e4ch/elm2/kicad/Mainboard.kicad_sch

## KiCad design kicad/Mainboard.kicad_sch (2026-03-01)

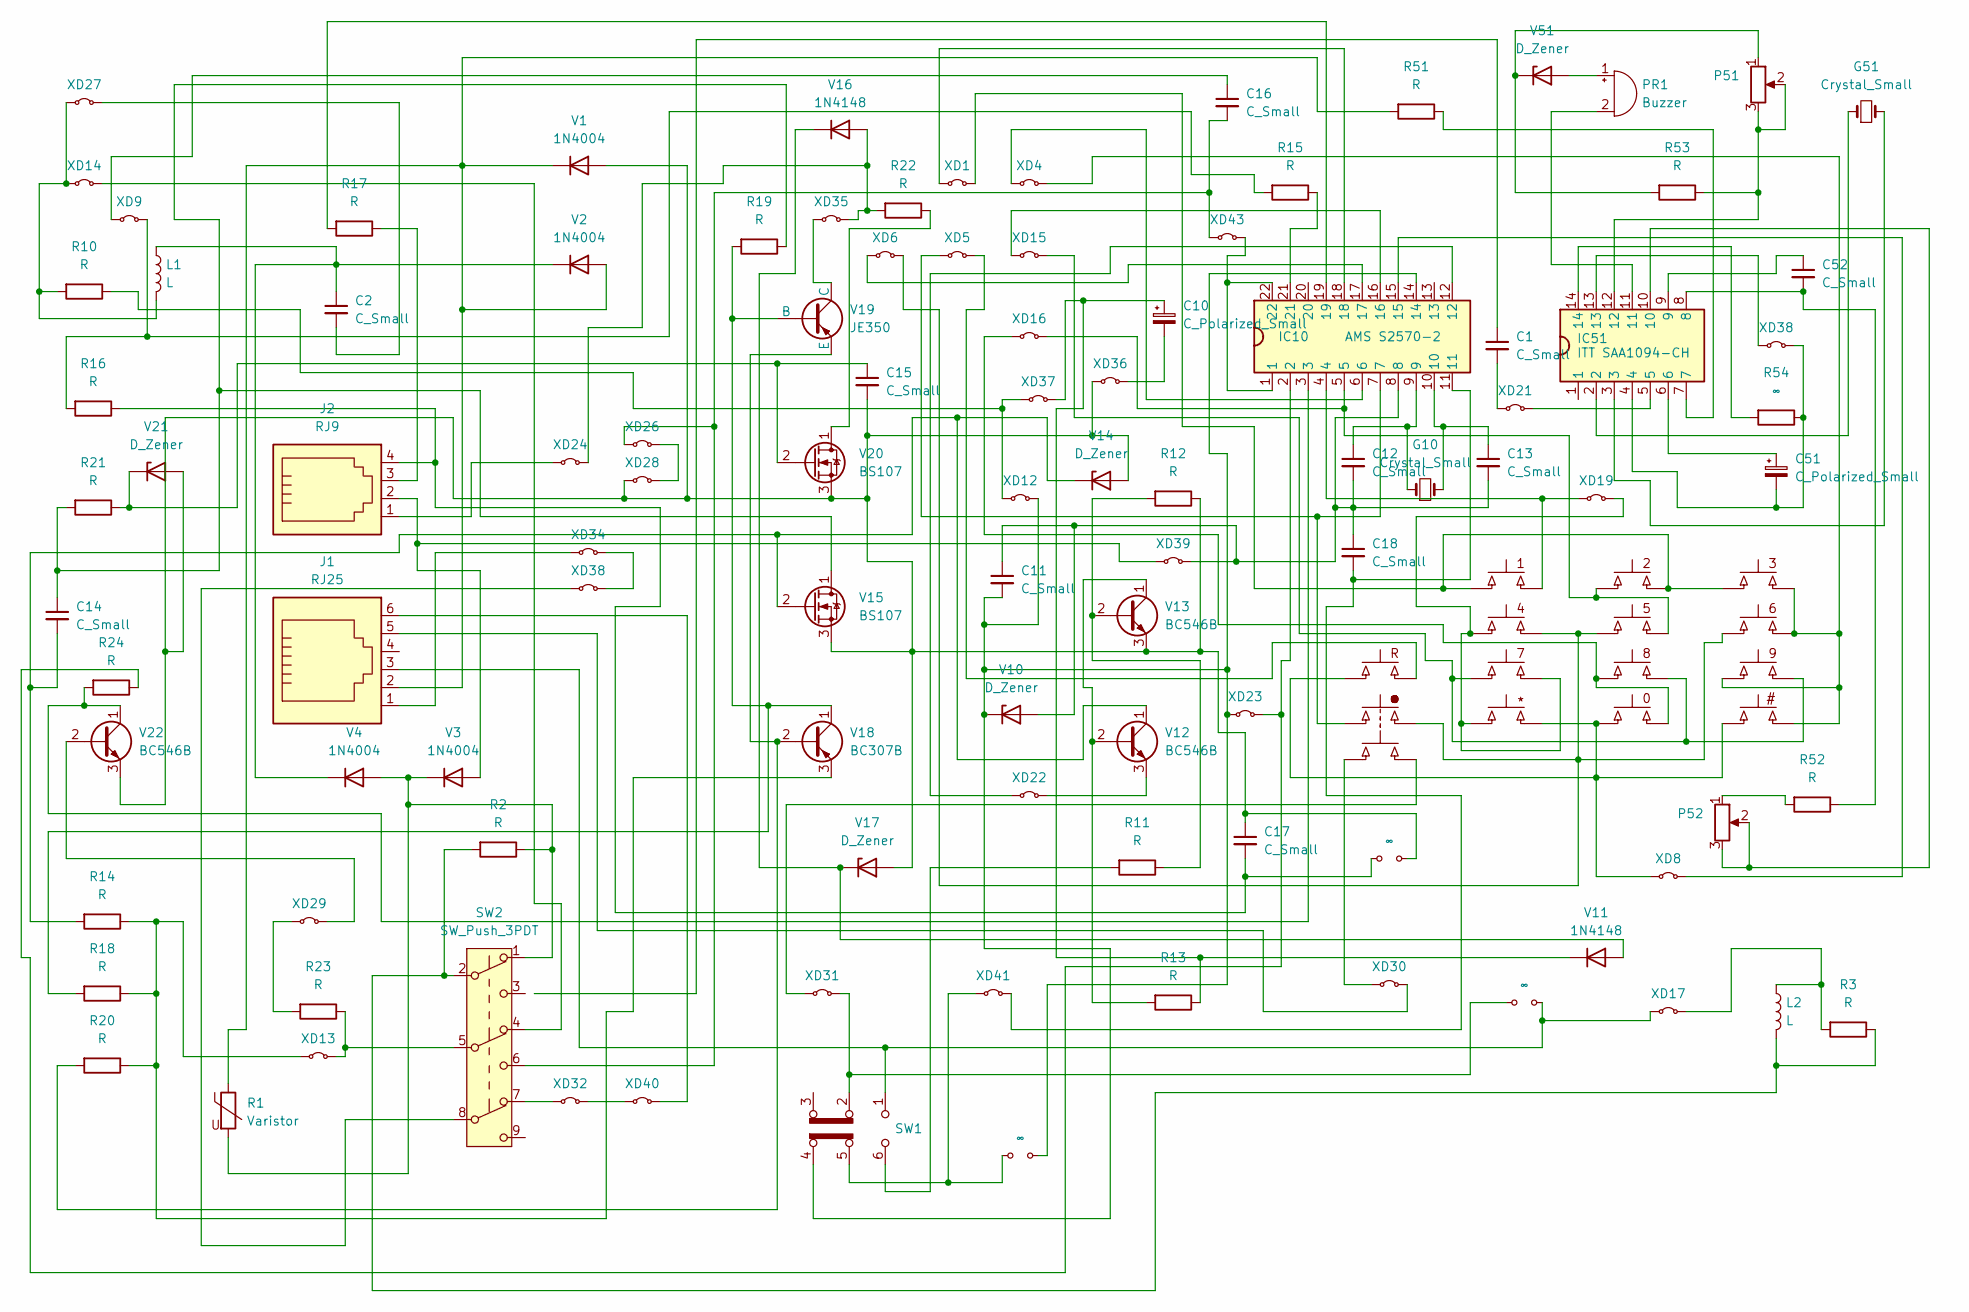
[picture p8: schematic Mainboard.kicad_sch]

Parts:
C1, C2, C11, C12, C13, C14, C15, C16, C17, C18, C52: C_Small
C10, C51: C_Polarized_Small
G10, G51: Crystal_Small
IC10: AMS S2570-2
IC51: ITT SAA1094-CH
J1: RJ25
J2: RJ9
KEYPAD1: SW_KEYPAD_PHONE_ELM2
L1, L2: L
P51, P52: (no value)
PR1: Buzzer
R1: Varistor
R2, R3, R10, R11, R12, R13, R14, R15, R16, R17, R18, R19, R20, R21, R22, R23, R24, R51, R52, R53: R
R54: ∞
SW1: SW_Slide_DPDT_horizontal
SW2: SW_Push_3PDT
V1, V2, V3, V4: 1N4004; D_DO-41_SOD81_P10.16mm_Horizontal
V10, V14, V17, V21, V51: D_Zener
V11, V16: 1N4148; D_DO-35_SOD27_P7.62mm_Horizontal
V12, V13, V22: BC546B; TO-92_Inline
V15, V20: BS107; TO-92_Inline
V18: BC307B; TO-92_Inline
V19: JE350
XD1, XD4, XD5, XD6, XD8, XD9, XD12, XD13, XD14, XD15, XD16, XD17, XD19, XD21, XD22, XD23, XD24, XD26, XD27, XD28, XD29, XD30, XD31, XD32, XD34, XD35, XD36, XD37, XD38, XD39, XD40, XD41, XD43: (no value)

Connections:
unnamed: C1.2, XD21.1 (A)
unnamed: C2.1, L1.1, V2.1 (K), V4.1 (K)
unnamed: C2.2, XD27.2 (B)
unnamed: C10.1, R13.1, V11.1 (K), XD37.2 (B)
unnamed: C10.2, XD36.2 (B)
unnamed: C11.1, C12.2, C13.2, C18.1, IC10.8, V10.2 (A), XD39.2 (B)
unnamed: C11.2, IC10.14, SW1.4 (A), V10.1 (K), XD12.2 (B), XD23.1 (A)
unnamed: C12.1, G10.1, IC10.9
unnamed: C13.1, G10.2, IC10.10
unnamed: C14.1, R19.1, R21.2, V15.1 (D)
unnamed: C14.2, R14.2, V12.1 (C), V14.1 (K), V15.2 (G)
unnamed: C15.1, R21.1, V20.2 (G), V21.1 (K)
unnamed: C15.2, C17.1, R12.1, V1.2 (A), V13.3 (E), V14.2 (A), V15.3 (S), V17.2 (A), V20.3 (S), V21.2 (A), V22.3 (E), XD28.1 (A), XD36.1 (A)
unnamed: C16.1, XD9.1 (A)
unnamed: C16.2, SW2.6 (C), XD26.1 (A), XD43.1 (A)
unnamed: C17.2, J2.4, R16.1
unnamed: C18.2, IC10.11, XD41.2 (B)
unnamed: C51.1, IC51.6
unnamed: C51.2, IC51.4, R54.1, XD38.2 (B)
unnamed: C52.1, IC51.9
unnamed: C52.2, IC51.8, R52.1
unnamed: G51.1, IC51.2
unnamed: G51.2, IC51.3
unnamed: IC10.1, IC10.22, XD43.2 (B)
unnamed: IC10.2, R24.1, XD23.2 (B)
unnamed: IC10.3, R24.2, V22.1 (C)
unnamed: IC10.4, KEYPAD1.3 (B), KEYPAD1.4 (B), XD19.1 (A)
unnamed: IC10.5, KEYPAD1.1 (A), KEYPAD1.2 (A), KEYPAD1.3 (B), KEYPAD1.4 (B), XD16.2 (B)
unnamed: IC10.6, XD4.1 (A)
unnamed: IC10.7, KEYPAD1.1 (A), KEYPAD1.2 (A), XD5.1 (A)
unnamed: IC10.12, XD22.1 (A)
unnamed: IC10.15, XD8.2 (B)
unnamed: IC10.16, XD15.1 (A)
unnamed: IC10.17, XD6.1 (A)
unnamed: IC10.18, XD1.1 (A)
unnamed: IC10.19, R17.2
unnamed: IC10.21, R15.1
unnamed: IC51.5, XD21.2 (B)
unnamed: IC51.7, R51.1
unnamed: IC51.10, P52.2, P52.3
unnamed: IC51.11, PR1.2 (-)
unnamed: IC51.12, P51.2, P51.3, R53.1
unnamed: IC51.13, XD38.1 (A)
unnamed: IC51.14, R54.2
unnamed: J1.1, XD34.1 (A)
unnamed: J1.2, R1.1, R51.2, V1.1 (K), V2.2 (A)
unnamed: J1.3, SW1.1 (A), XD17.1 (A)
unnamed: J1.5, XD30.2 (B)
unnamed: J1.6, XD40.2 (B)
unnamed: J2.1, XD24.1 (A)
unnamed: J2.2, V3.2 (A), XD39.1 (A)
unnamed: J2.3, R17.1
unnamed: KEYPAD1.1 (A), KEYPAD1.2 (A), KEYPAD1.3 (B), KEYPAD1.4 (B), XD1.2 (B), XD4.2 (B), XD6.2 (B), XD8.1 (A), XD15.2 (B), XD16.1 (A), XD19.2 (B), XD30.1 (A)
unnamed: KEYPAD1.3 (B), KEYPAD1.4 (B), XD5.2 (B), XD31.1 (A)
unnamed: L1.2, R10.2, XD14.1 (A), XD27.1 (A)
unnamed: L2.1, R3.2, XD17.2 (B)
unnamed: L2.2, R2.2, R3.1, SW2.2 (B)
unnamed: P51.1, R53.2, V51.1 (K)
unnamed: P52.1, R52.2
unnamed: PR1.1 (+), V51.2 (A)
unnamed: R1.2, R2.1, SW2.1 (A), V3.1 (K), V4.2 (A)
unnamed: R10.1, XD12.1 (A), XD37.1 (A)
unnamed: R11.1, R12.2, V13.2 (B)
unnamed: R11.2, SW1.6 (C)
unnamed: R13.2, V12.2 (B), V13.1 (C)
unnamed: R14.1, R18.1, R20.1, V18.3 (E), XD13.1 (A)
unnamed: R15.2, R16.2, XD9.2 (B)
unnamed: R18.2, R19.2, V18.1 (C), V19.2 (B)
unnamed: R20.2, V18.2 (B), V19.3 (E)
unnamed: R22.1, V20.1 (D)
unnamed: R22.2, V16.2 (A), XD24.2 (B), XD35.2 (B)
unnamed: R23.1, SW2.5 (B), XD13.2 (B)
unnamed: R23.2, XD29.1 (A)
unnamed: SW1.2 (B), XD31.2 (B)
unnamed: SW1.5 (B), XD41.1 (A)
unnamed: SW2.4 (A), XD14.2 (B)
unnamed: SW2.7 (A), XD32.1 (A)
unnamed: SW2.8 (B), XD38.1 (A)
unnamed: V11.2 (A), V16.1 (K), V17.1 (K)
unnamed: V12.3 (E), XD22.2 (B)
unnamed: V19.1 (C), XD35.1 (A)
unnamed: V22.2 (B), XD29.2 (B)
unnamed: XD26.2 (B), XD28.2 (B)
unnamed: XD32.2 (B), XD40.1 (A)
unnamed: XD34.2 (B), XD38.2 (B)
