e4ch/elm2/kicad/headset.kicad_sch

## KiCad design kicad/headset.kicad_sch (2026-03-01)

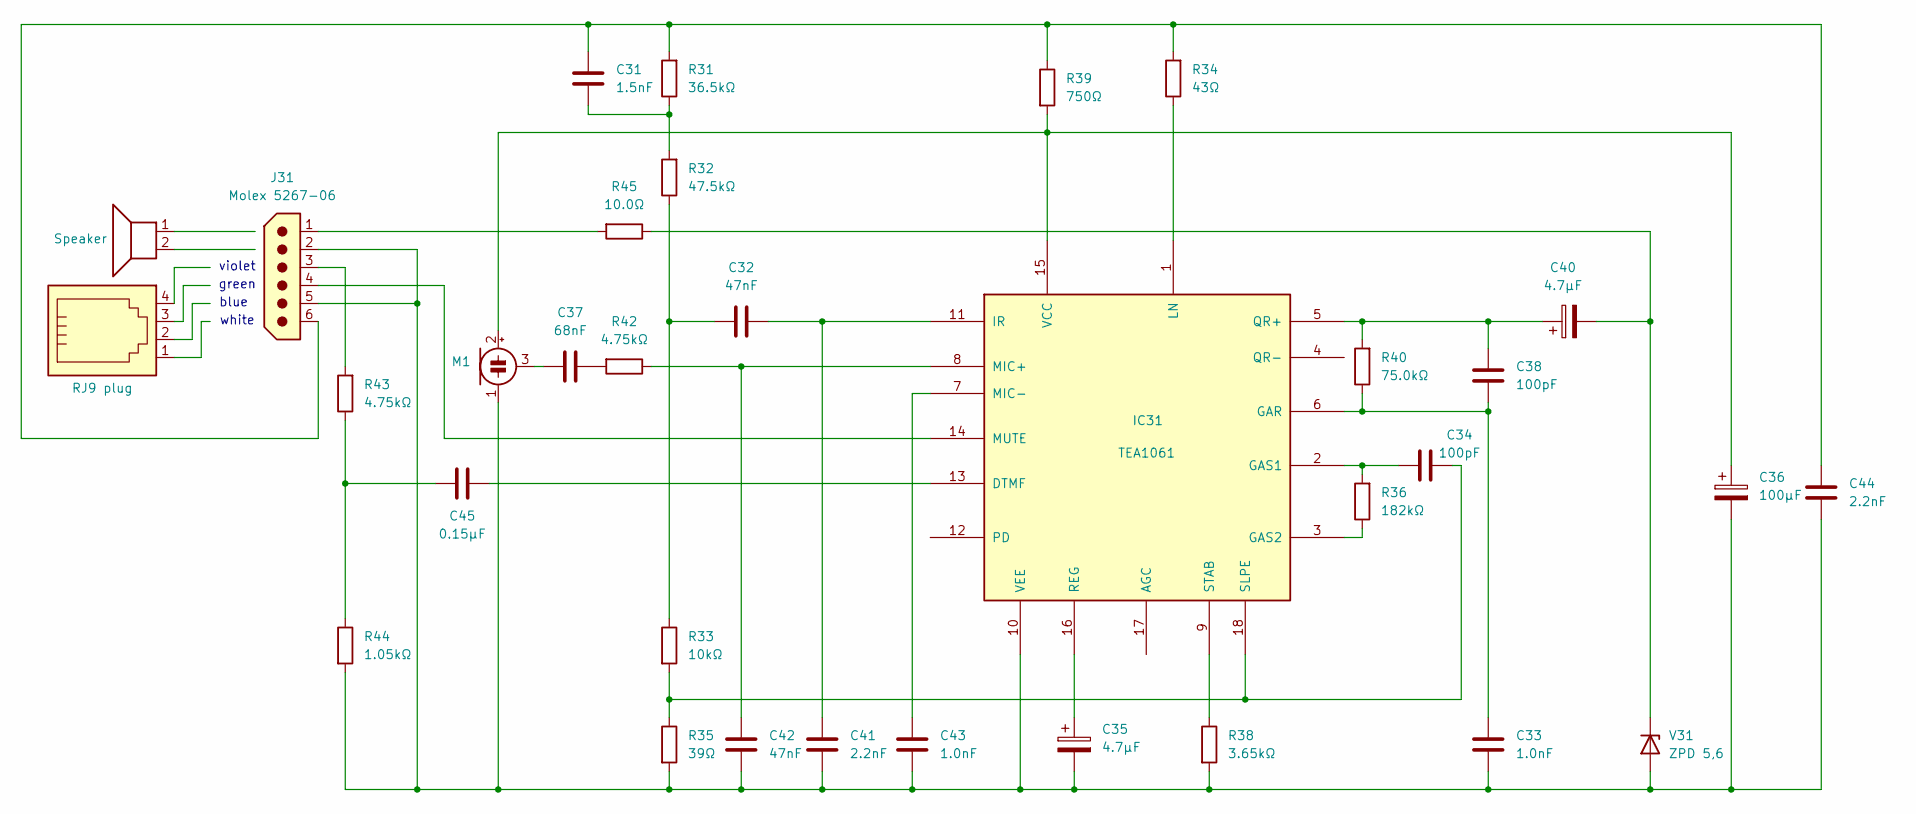
[picture p9: schematic headset.kicad_sch]

Parts:
C31: 1.5nF
C32, C42: 47nF
C33, C43: 1.0nF
C34, C38: 100pF
C35, C40: 4.7μF
C36: 100μF
C37: 68nF
C41, C44: 2.2nF
C45: 0.15μF
IC31: TEA1061; DIP-18_W7.62mm
J3: RJ9 plug
J31: Molex 5267-06; Molex_SPOX_5267-06A_1x06_P2.50mm_Vertical
LS1: Speaker
M1: Mic_3pin
R31: 36.5kΩ
R32: 47.5kΩ
R33: 10kΩ
R34: 43Ω
R35: 39Ω
R36: 182kΩ
R38: 3.65kΩ
R39: 750Ω
R40: 75.0kΩ
R42, R43: 4.75kΩ
R44: 1.05kΩ
R45: 10.0Ω
V31: ZPD 5,6

Connections:
unnamed: C31.1, C44.1, J31.6, R31.2, R34.2, R39.1
unnamed: C31.2, R31.1, R32.2
unnamed: C32.1, R32.1, R33.1
unnamed: C32.2, C41.1, IC31.11 (IR)
unnamed: C33.1, C38.2, IC31.6 (GAR), R40.1
unnamed: C33.2, C35.2, C36.2, C41.2, C42.2, C43.2, C44.2, IC31.10 (VEE), J31.2, J31.5, M1.1 (-), R35.2, R38.2, R44.2, V31.2 (A)
unnamed: C34.1, IC31.2 (GAS1), R36.2
unnamed: C34.2, IC31.18 (SLPE), R33.2, R35.1
unnamed: C35.1, IC31.16 (REG)
unnamed: C36.1, IC31.15 (VCC), M1.2 (+), R39.2
unnamed: C37.1, M1.3
unnamed: C37.2, R42.2
unnamed: C38.1, C40.1, IC31.5 (QR+), R40.2
unnamed: C40.2, R45.1, V31.1 (K)
unnamed: C42.1, IC31.8 (MIC+), R42.1
unnamed: C43.1, IC31.7 (MIC-)
unnamed: C45.1, IC31.13 (DTMF)
unnamed: C45.2, R43.1, R44.1
unnamed: IC31.1 (LN), R34.1
unnamed: IC31.3 (GAS2), R36.1
unnamed: IC31.9 (STAB), R38.1
unnamed: IC31.14 (MUTE), J31.4
unnamed: J31.1, R45.2
unnamed: J31.3, R43.2

Notes on the sheet:
white
green
violet
blue
